saraflorean/OpenBook_TSC/Images/3D_view_top.jpeg

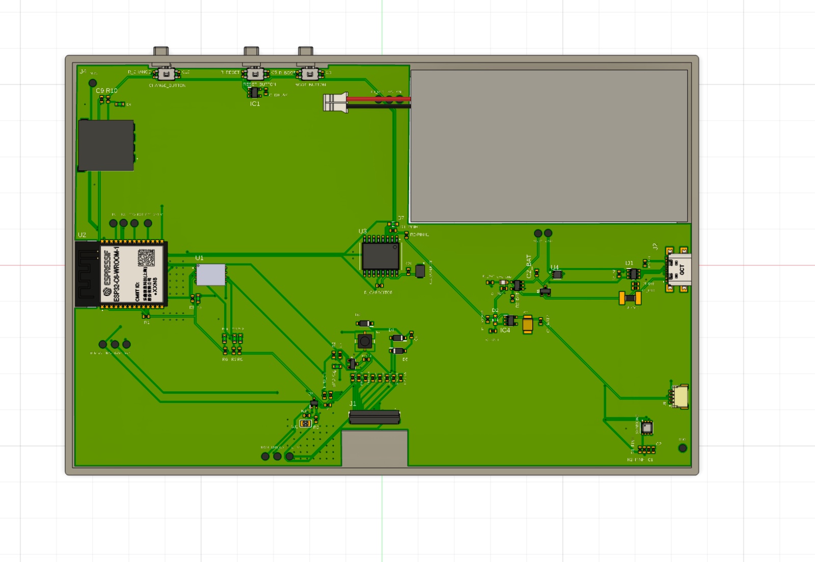
Images/3D_view_top.jpeg
