saraflorean/OpenBook_TSC/Images/Bottom_Routing.jpeg

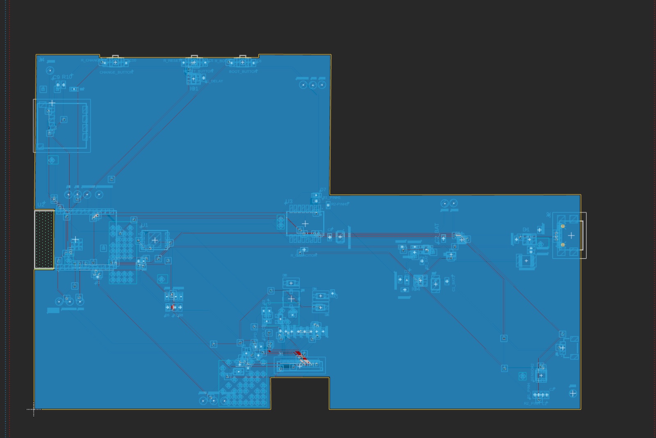
Images/Bottom_Routing.jpeg
