saraflorean/OpenBook_TSC/Images/Display.jpeg

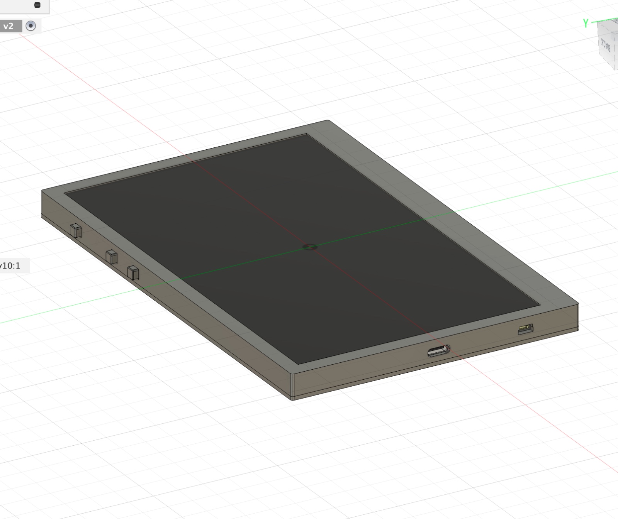
Images/Display.jpeg
